liulizhi1031/ProjectEvolution/3D_Model/V0.1_3D_Model/3.5寸屏幕模块/img_dev_2.png

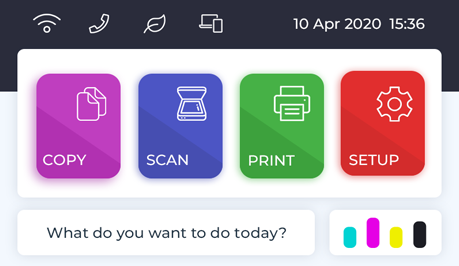
3D_Model/V0.1_3D_Model/3.5寸屏幕模块/img_dev_2.png
