liulizhi1031/ProjectEvolution/3D_Model/V0.1_3D_Model/Frsky-R9M/Render.jpg

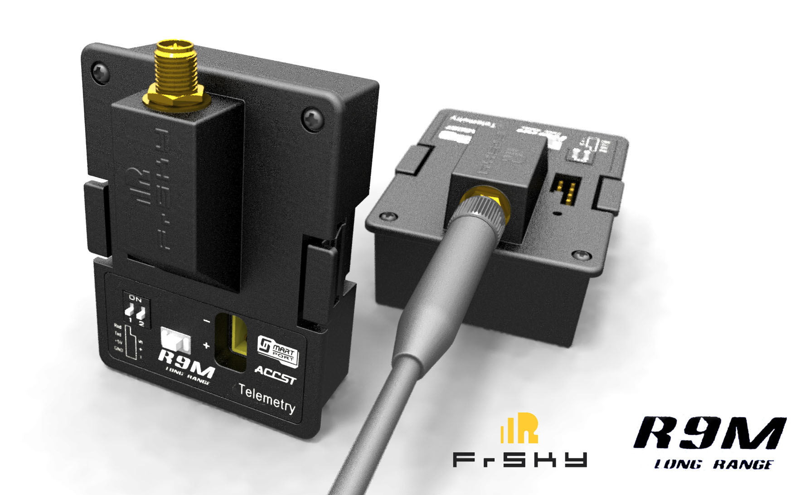
3D_Model/V0.1_3D_Model/Frsky-R9M/Render.jpg
