liulizhi1031/ProjectEvolution/3D_Model/V0.1_3D_Model/GPS-TS100/IMG_20190112_132327.jpg

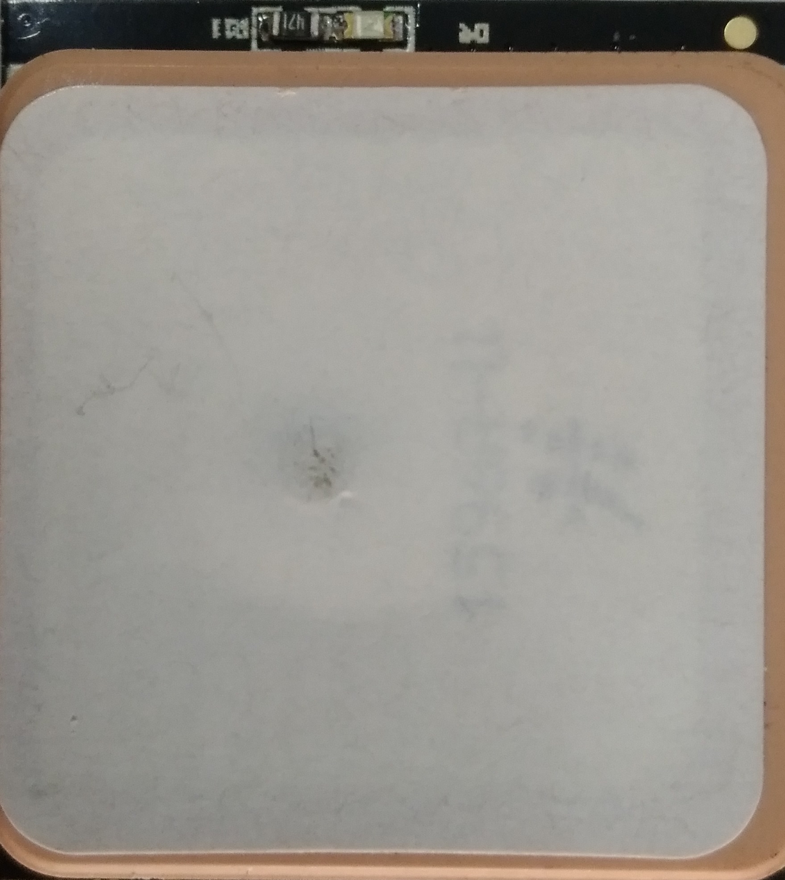
3D_Model/V0.1_3D_Model/GPS-TS100/IMG_20190112_132327.jpg
