liulizhi1031/ProjectEvolution/3D_Model/V0.1_3D_Model/SWD模块/副板正面.JPG

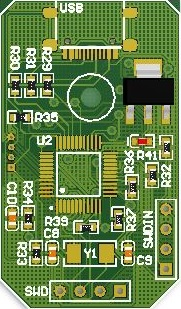
3D_Model/V0.1_3D_Model/SWD模块/副板正面.JPG
