liulizhi1031/ProjectEvolution/Reference/3.5inch_MCU_LCD/3.5inch_MRB3511_Size.png

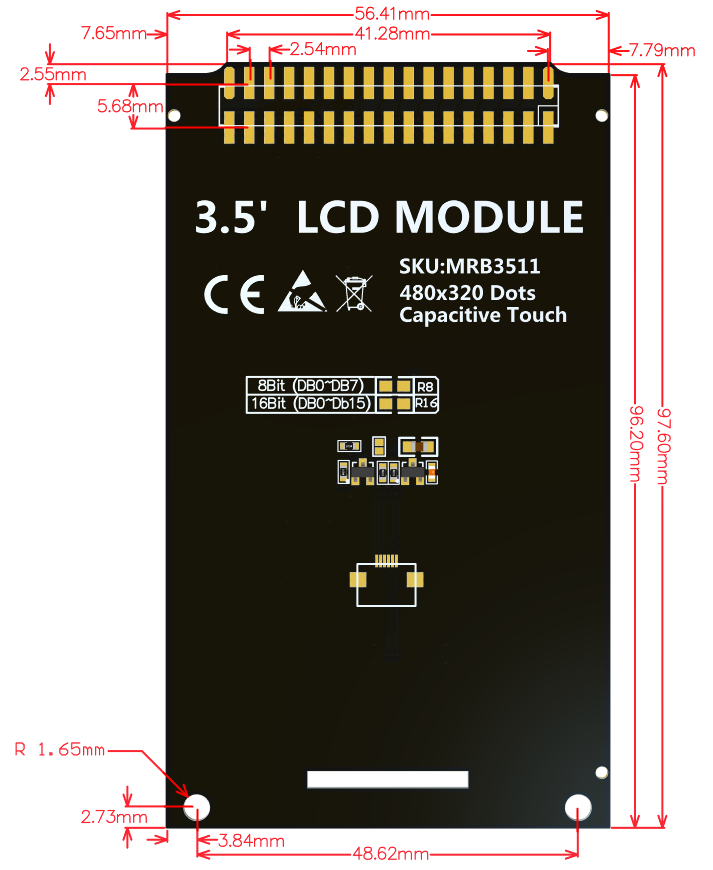
Reference/3.5inch_MCU_LCD/3.5inch_MRB3511_Size.png
