liulizhi1031/ProjectEvolution/3D_Model/V0.1_3D_Model/GPS-TS100/GPS-TS100.SLDPRT

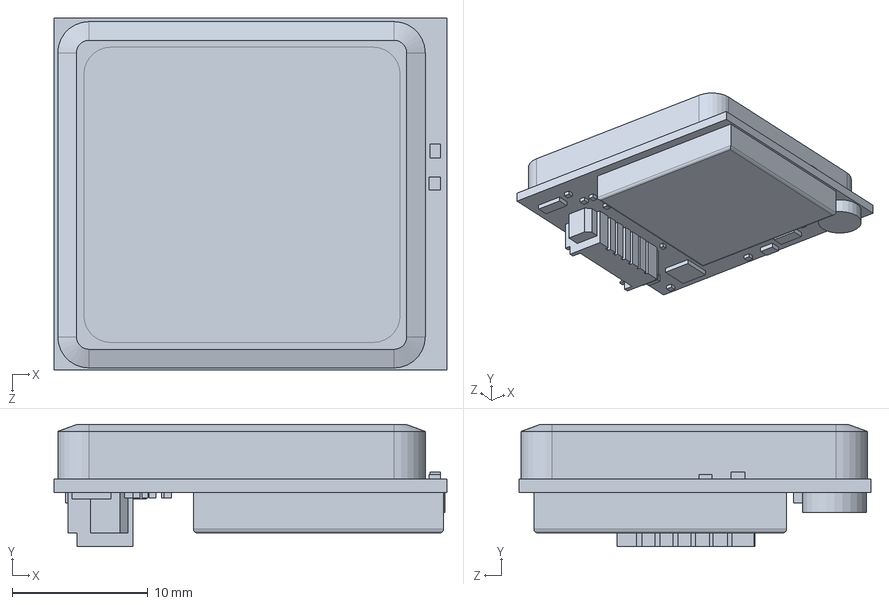
[picture p53: CAD file, 2021-01-28]
3D_Model/V0.1_3D_Model/GPS-TS100/GPS-TS100.SLDPRT
29.0 x 9.01 x 26.0 mm
