liulizhi1031/ProjectEvolution/3D_Model/V0.1_3D_Model/keyboard/滑动开关/滑动开关.SLDPRT

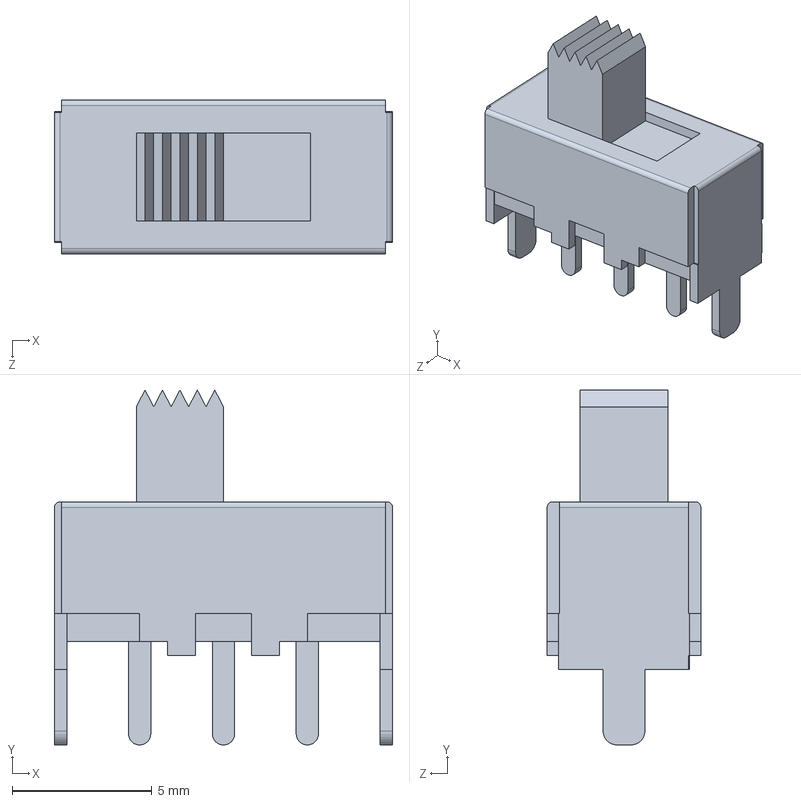
[picture p54: CAD file, 2021-01-28]
3D_Model/V0.1_3D_Model/keyboard/滑动开关/滑动开关.SLDPRT
12.1 x 12.7 x 5.50 mm
