liulizhi1031/ProjectEvolution/3D_Model/V0.1_3D_Model/mini_MP3/MP3_mini.SLDPRT

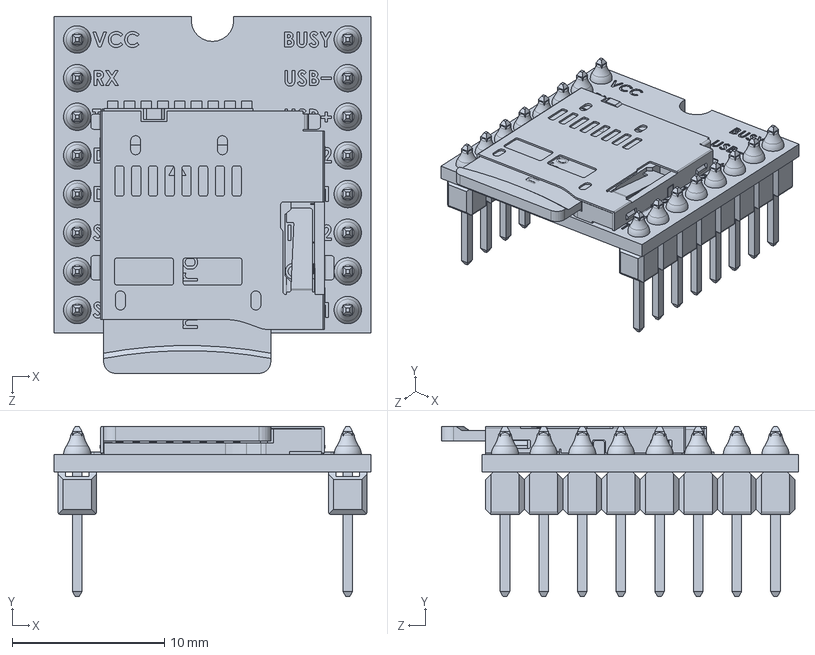
[picture p55: CAD file, 2021-01-28]
3D_Model/V0.1_3D_Model/mini_MP3/MP3_mini.SLDPRT
20.8 x 11.2 x 23.5 mm
