liulizhi1031/ProjectEvolution/3D_Model/V0.1_3D_Model/NRF24l01/E01-ML01DP5.SLDPRT

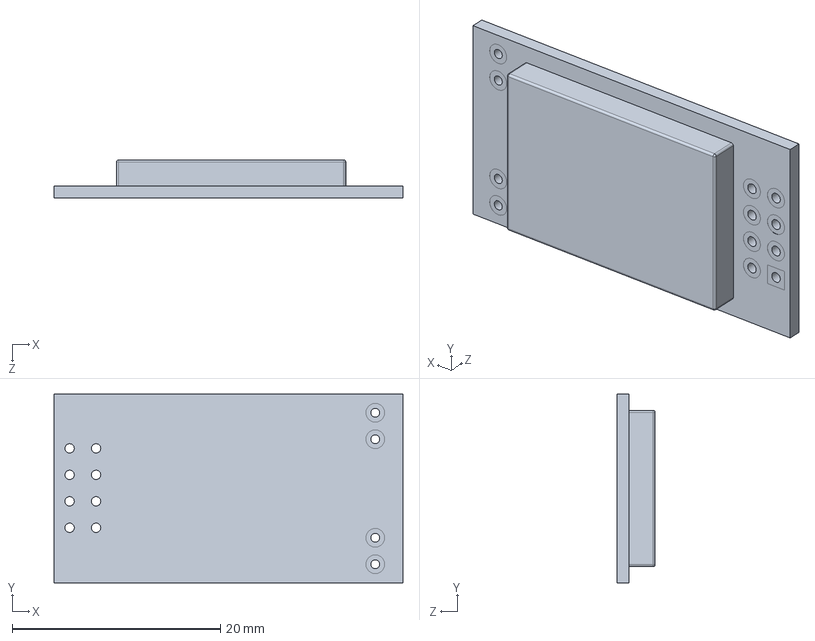
[picture p56: CAD file, 2021-01-28]
3D_Model/V0.1_3D_Model/NRF24l01/E01-ML01DP5.SLDPRT
33.5 x 18.1 x 3.69 mm
