liulizhi1031/ProjectEvolution/3D_Model/V0.1_3D_Model/STL/ANTENNA_STAND.STL

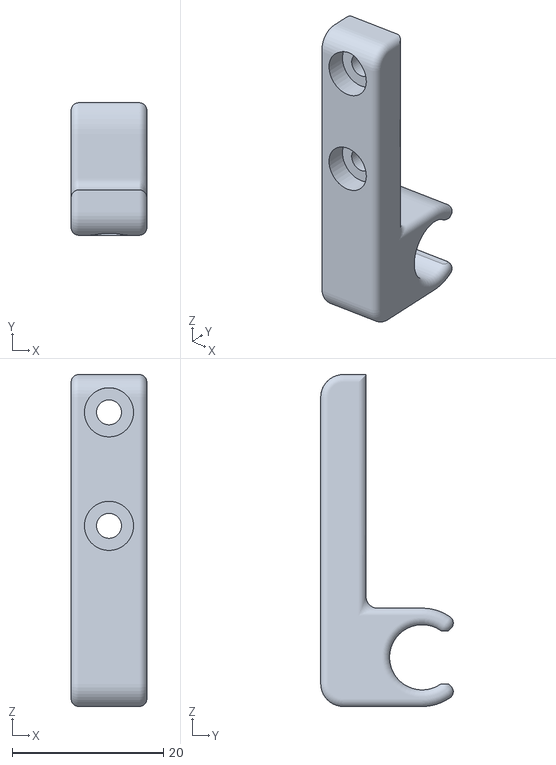
[picture p58: CAD file, 2021-02-08]
3D_Model/V0.1_3D_Model/STL/ANTENNA_STAND.STL
10.0 x 17.5 x 43.9
