liulizhi1031/ProjectEvolution/3D_Model/V0.1_3D_Model/SWD模块/1.27mmHeader.SLDPRT

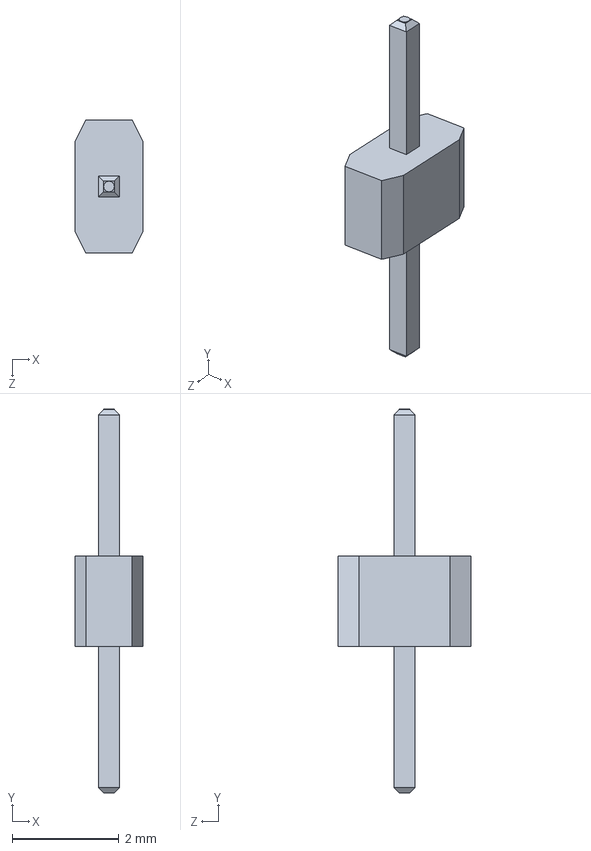
[picture p59: CAD file, 2021-01-28]
3D_Model/V0.1_3D_Model/SWD模块/1.27mmHeader.SLDPRT
1.27 x 7.21 x 2.50 mm
