liulizhi1031/ProjectEvolution/3D_Model/V0.1_3D_Model/SWD模块/stm32f103c8t6-1.snapshot.1/STM32-LQFP48.SLDPRT

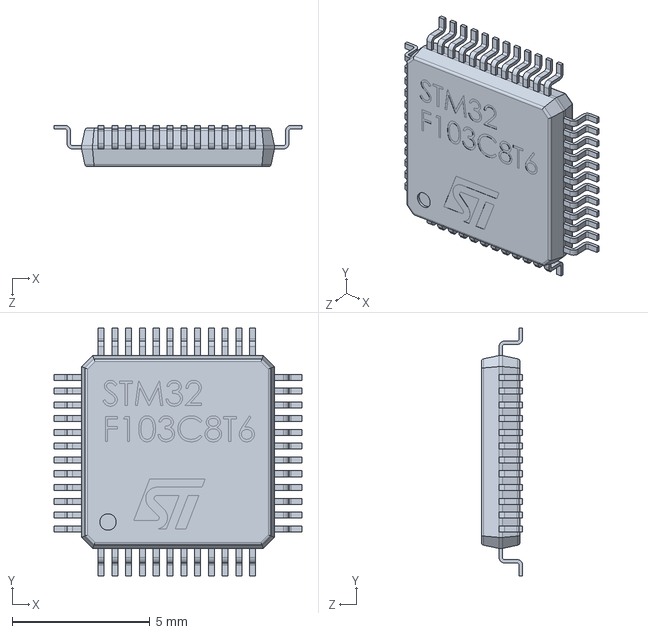
[picture p61: CAD file, 2021-01-28]
3D_Model/V0.1_3D_Model/SWD模块/stm32f103c8t6-1.snapshot.1/STM32-LQFP48.SLDPRT
9.00 x 9.00 x 1.50 mm
