liulizhi1031/ProjectEvolution/3D_Model/V0.1_3D_Model/SWD模块/USB_TYPE_C/USB Type C Port (SMD Type).STEP

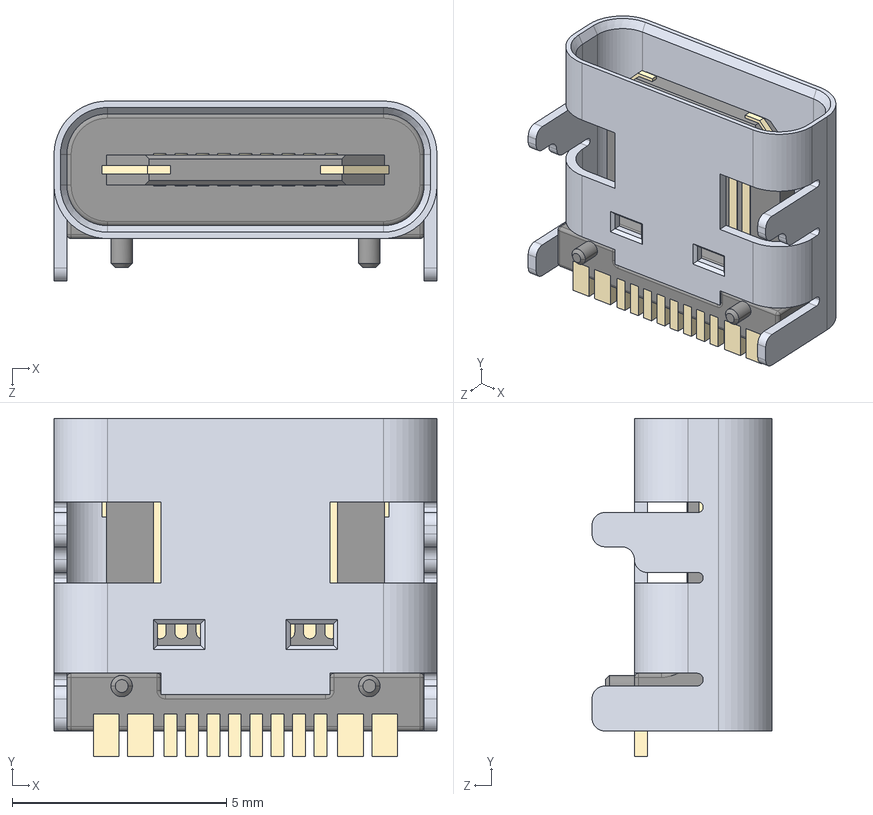
[picture p62: CAD file, 2021-01-28]
3D_Model/V0.1_3D_Model/SWD模块/USB_TYPE_C/USB Type C Port (SMD Type).STEP
8.94 x 7.90 x 4.20 mm
