liulizhi1031/ProjectEvolution/3D_Model/V0.1_3D_Model/下壳.SLDPRT

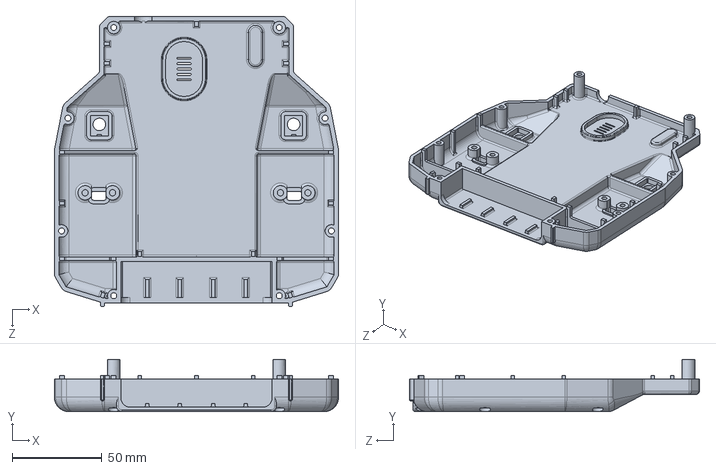
[picture p63: CAD file, 2021-02-08]
3D_Model/V0.1_3D_Model/下壳.SLDPRT
158.0 x 29.0 x 161.2 mm
