liulizhi1031/ProjectEvolution/3D_Model/V0.1_3D_Model/对比模型/Mavic Air 2 Controller.SLDPRT

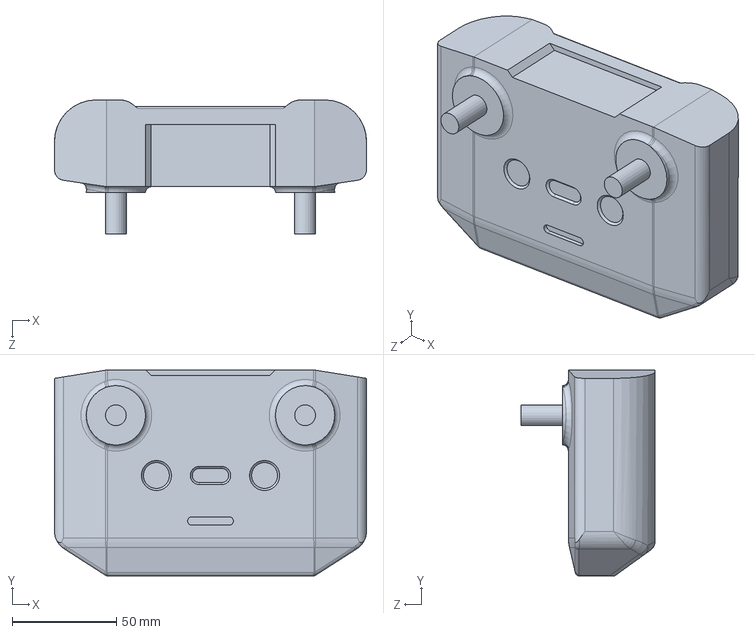
[picture p64: CAD file, 2021-01-28]
3D_Model/V0.1_3D_Model/对比模型/Mavic Air 2 Controller.SLDPRT
150.0 x 99.0 x 64.5 mm
