liulizhi1031/ProjectEvolution/3D_Model/V0.1_3D_Model/按键板/JST connector 1x3.SLDPRT

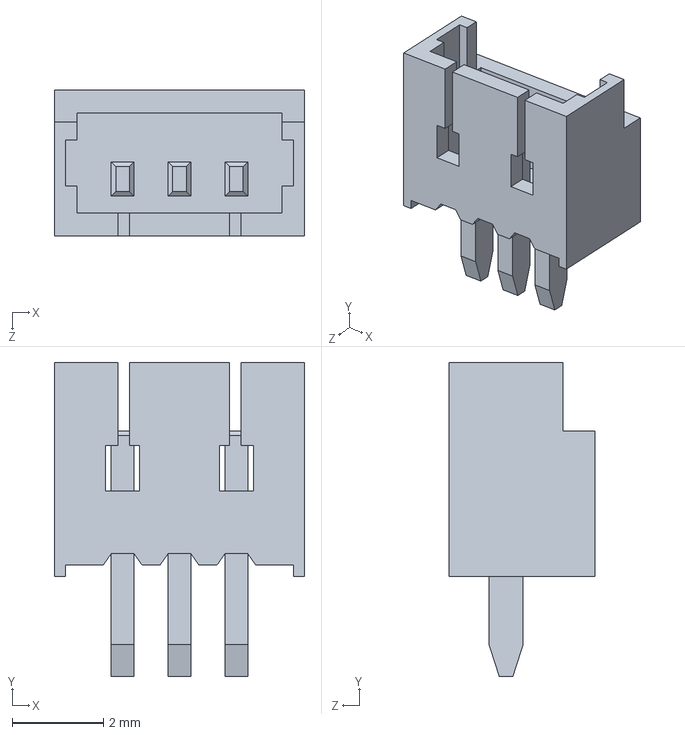
[picture p65: CAD file, 2021-01-28]
3D_Model/V0.1_3D_Model/按键板/JST connector 1x3.SLDPRT
5.50 x 6.90 x 3.20 mm
