liulizhi1031/ProjectEvolution/3D_Model/V0.1_3D_Model/电位器10K/Turn Knob.SLDPRT

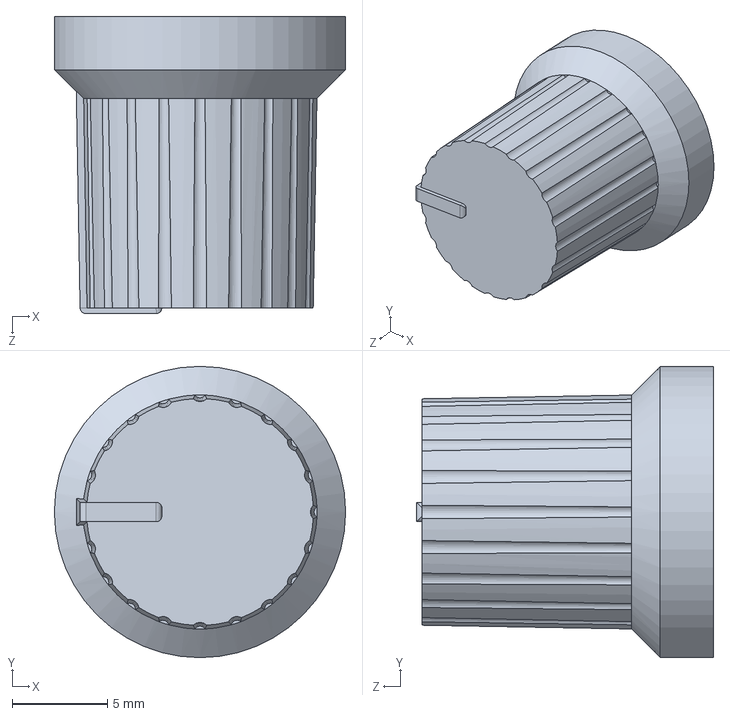
[picture p66: CAD file, 2021-01-30]
3D_Model/V0.1_3D_Model/电位器10K/Turn Knob.SLDPRT
15.3 x 15.3 x 15.6 mm
