liulizhi1031/ProjectEvolution/3D_Model/V0.1_3D_Model/航模摇杆T8SG/摇杆头.SLDPRT

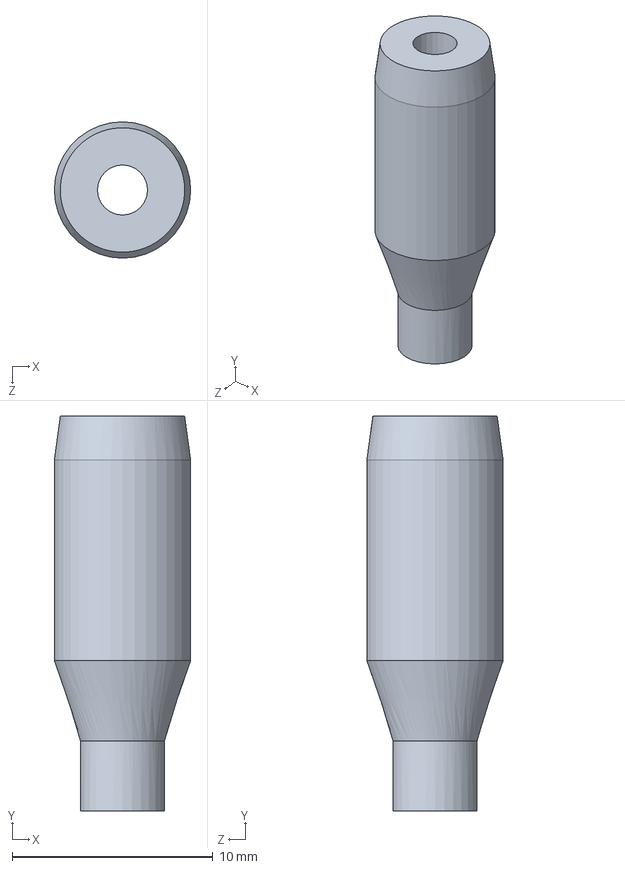
[picture p67: CAD file, 2021-01-28]
3D_Model/V0.1_3D_Model/航模摇杆T8SG/摇杆头.SLDPRT
6.80 x 19.7 x 6.80 mm
