liulizhi1031/ProjectEvolution/PCB/V0.1_PCB/CoreBoard/coreboardV0.1pcb.step

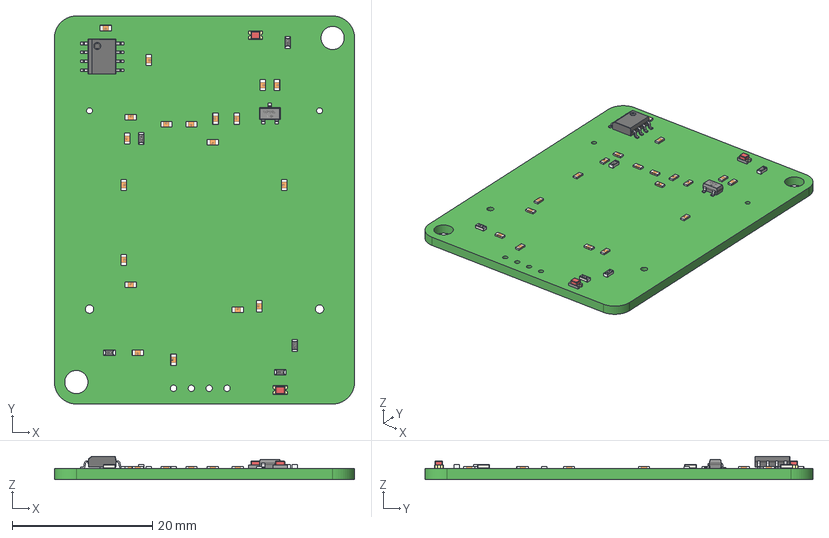
[picture p68: CAD file, 2021-01-28]
PCB/V0.1_PCB/CoreBoard/coreboardV0.1pcb.step
42.8 x 55.3 x 3.34 mm
Board
User_Library-SOIC-8-150_pin_SOIC_SO-150_1 x 8
User_Library-SOIC-8-150_SOIC_150_SOIC_5X4_1
User_Library-0603_SMD_Capacitor x 19
SOT-23
User_Library-RES_1609-0603 x 5
User_Library-led_0805 x 2
