liulizhi1031/ProjectEvolution/PCB/V0.1_PCB/KeyBoard/keyboardV0.1.step

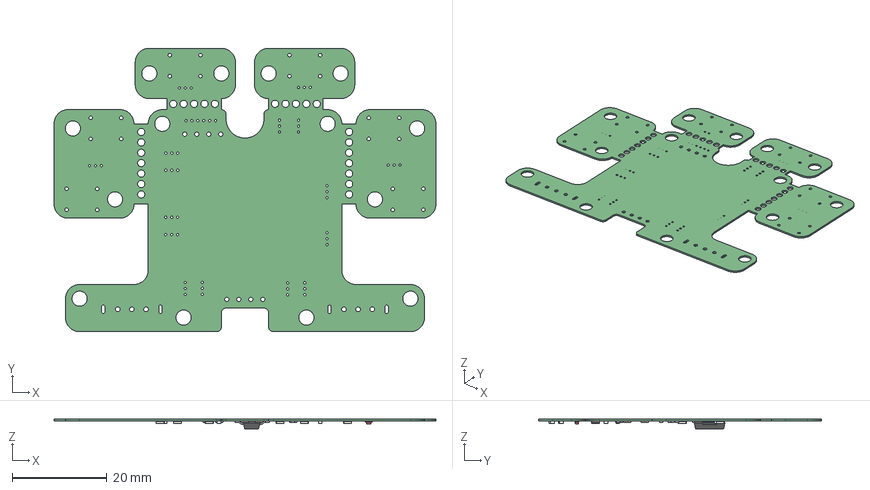
[picture p69: CAD file, 2021-01-28]
PCB/V0.1_PCB/KeyBoard/keyboardV0.1.step
80.8 x 60.0 x 2.05 mm
Board
User_Library-RES_1609-0603 x 14
User_Library-TO-223_1_1
User_Library-TO-223_2_1
User_Library-TO-223_3_1
User_Library-TO-223_4_1
User_Library-TO-223_5_1
User_Library-LED_0603_R_Pocket002
User_Library-LED_0603_R_Pad004
User_Library-LED_0603_R_Fillet
User_Library-LED_0603_R_Pocket001
User_Library-LED_0603_R_Pad
User_Library-0603_SMD_Capacitor x 13
