liulizhi1031/ProjectEvolution/3D_Model/V0.1_3D_Model/3.5寸屏幕模块/PIN254.SLDPRT

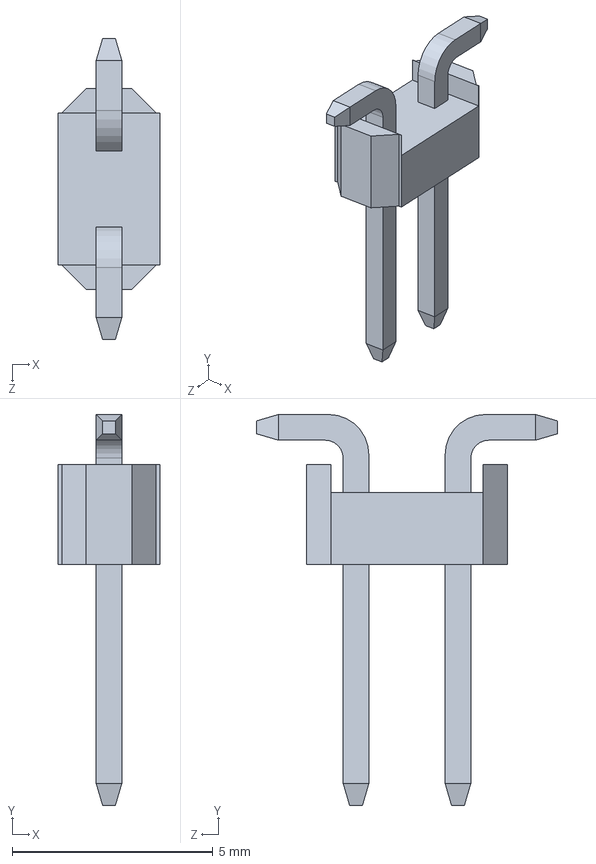
[picture p70: CAD file, 2021-01-28]
3D_Model/V0.1_3D_Model/3.5寸屏幕模块/PIN254.SLDPRT
2.54 x 9.74 x 7.50 mm
