liulizhi1031/ProjectEvolution/3D_Model/V0.1_3D_Model/keyboard/静音按键_.SLDPRT

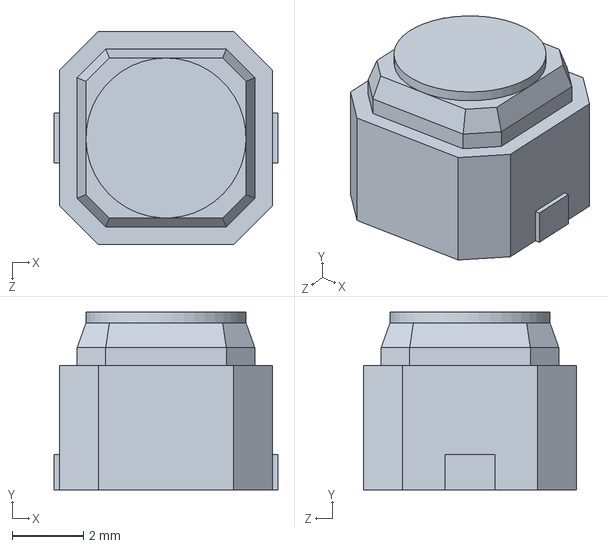
[picture p71: CAD file, 2021-01-28]
3D_Model/V0.1_3D_Model/keyboard/静音按键_.SLDPRT
6.30 x 5.00 x 6.00 mm
