liulizhi1031/ProjectEvolution/3D_Model/V0.1_3D_Model/NRF24l01/2.54MM_4_2PIN.SLDPRT

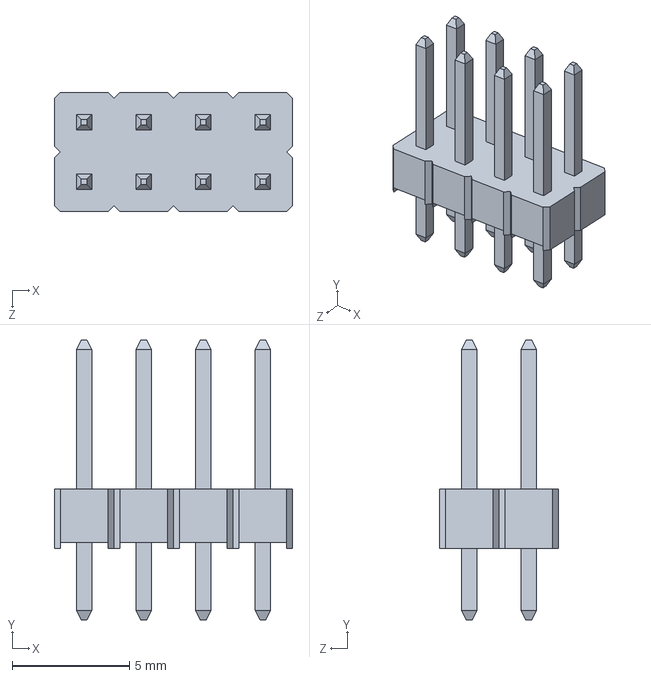
[picture p72: CAD file, 2021-01-28]
3D_Model/V0.1_3D_Model/NRF24l01/2.54MM_4_2PIN.SLDPRT
10.2 x 11.9 x 5.08 mm
