liulizhi1031/ProjectEvolution/3D_Model/V0.1_3D_Model/NRF24l01/棒状天线/Antenna.STEP

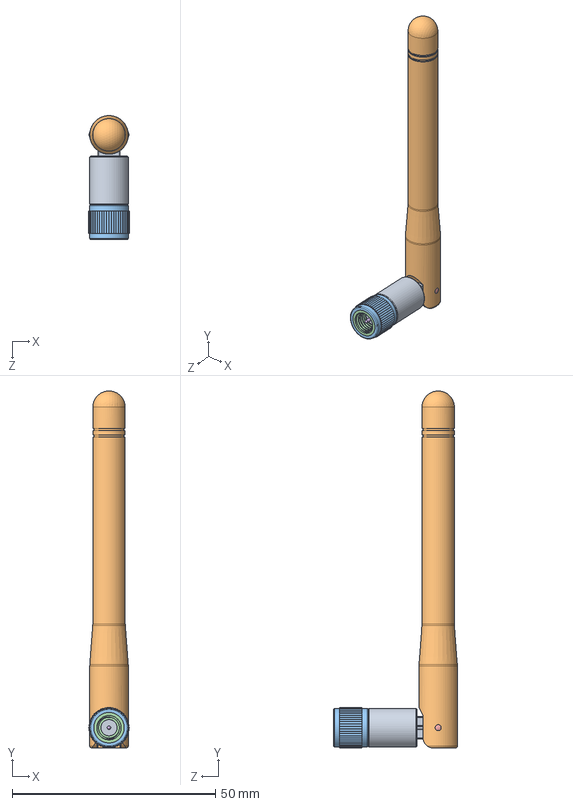
[picture p73: CAD file, 2021-01-28]
3D_Model/V0.1_3D_Model/NRF24l01/棒状天线/Antenna.STEP
10.00 x 87.9 x 30.5 mm
Bottom_Radio_Antenna
Top_Radio_Antenna
Screw_Radio_Antenna
Insert_Radio_Antenna
Pin_Radio_Antenna x 2
Wire_Top_Radio_Antenna
Wire_Radio_Antenna
