liulizhi1031/ProjectEvolution/3D_Model/V0.1_3D_Model/STL/BATTERY_COVER.STL

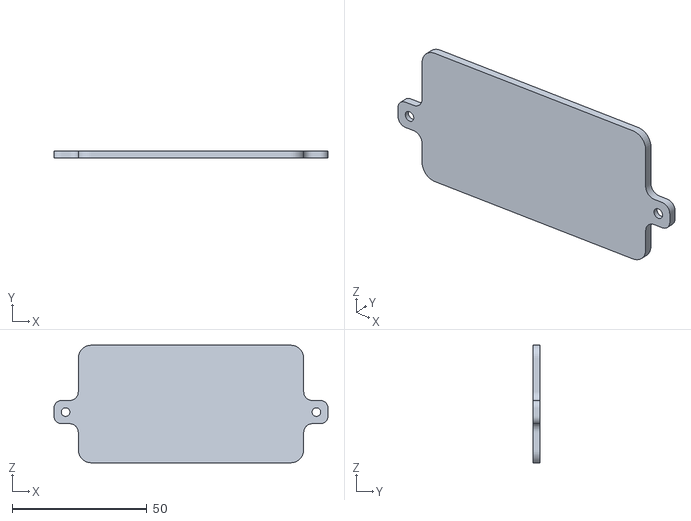
[picture p74: CAD file, 2021-02-05]
3D_Model/V0.1_3D_Model/STL/BATTERY_COVER.STL
101.6 x 2.50 x 43.6
