liulizhi1031/ProjectEvolution/3D_Model/V0.1_3D_Model/按键板/Tactal Switch -Thru (6mmx 6mmx5.0mm).SLDPRT

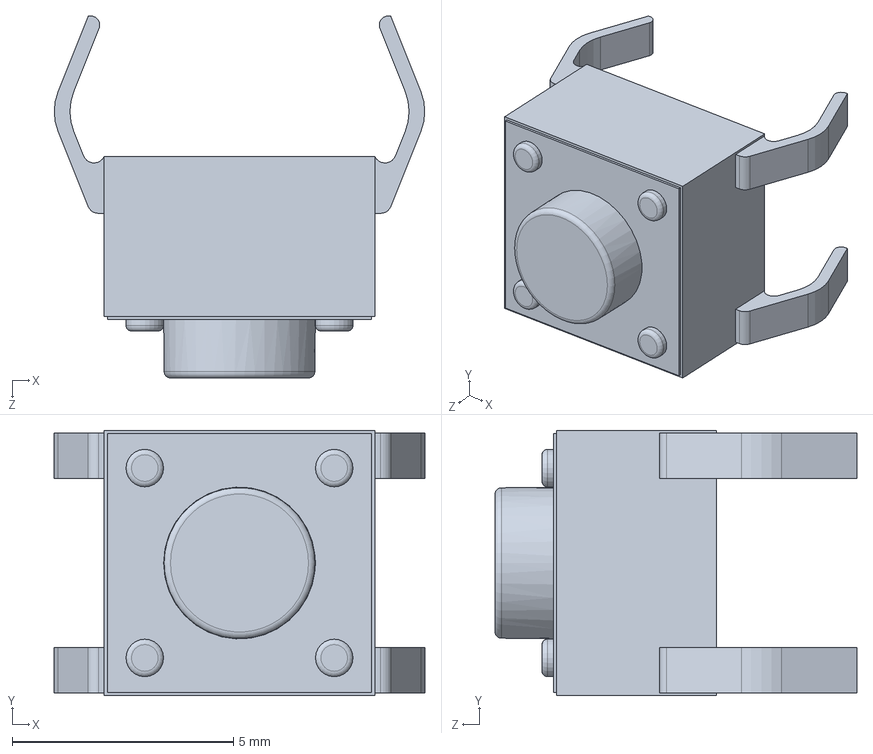
[picture p75: CAD file, 2021-01-28]
3D_Model/V0.1_3D_Model/按键板/Tactal Switch -Thru (6mmx 6mmx5.0mm).SLDPRT
8.37 x 5.99 x 8.18 mm
