liulizhi1031/ProjectEvolution/3D_Model/V0.1_3D_Model/电位器10K/PTD904.SLDPRT

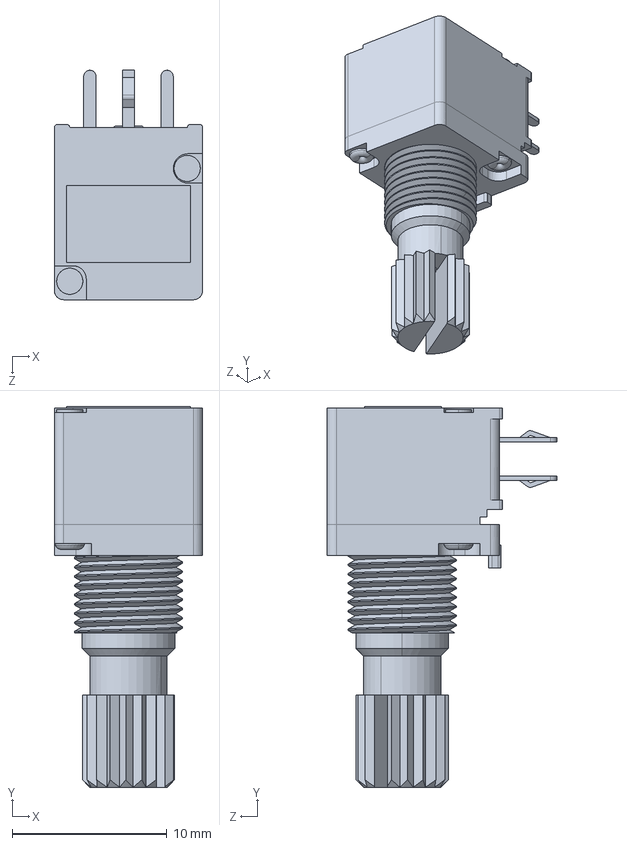
[picture p76: CAD file, 2021-01-28]
3D_Model/V0.1_3D_Model/电位器10K/PTD904.SLDPRT
9.60 x 24.6 x 14.9 mm
