liulizhi1031/ProjectEvolution/3D_Model/V0.1_3D_Model/航模摇杆T8SG/摇杆中间组件3.SLDPRT

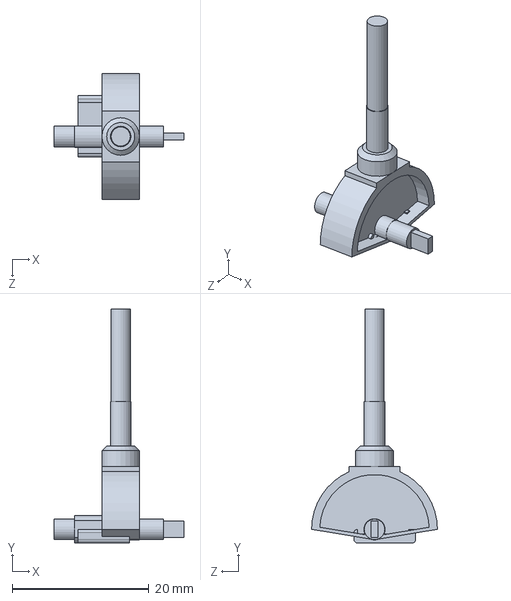
[picture p77: CAD file, 2021-01-28]
3D_Model/V0.1_3D_Model/航模摇杆T8SG/摇杆中间组件3.SLDPRT
19.0 x 34.2 x 18.4 mm
