liulizhi1031/ProjectEvolution/3D_Model/V0.1_3D_Model/Frsky-R9M/FrSky_R9M.SLDPRT

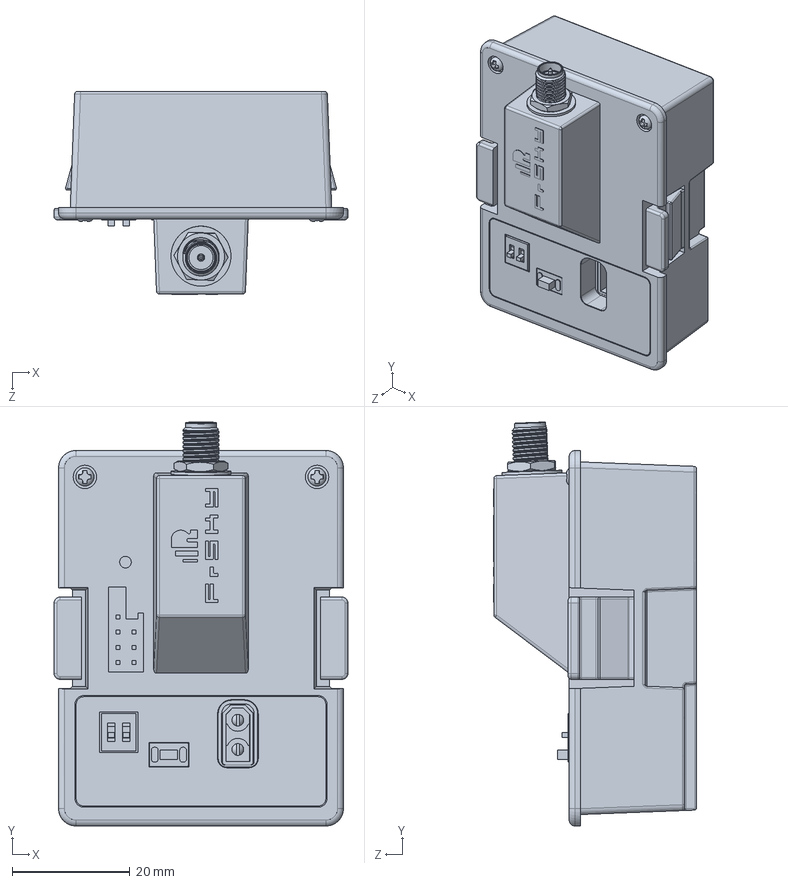
[picture p78: CAD file, 2021-01-28]
3D_Model/V0.1_3D_Model/Frsky-R9M/FrSky_R9M.SLDPRT
50.0 x 68.7 x 34.6 mm
