liulizhi1031/ProjectEvolution/3D_Model/V0.1_3D_Model/NRF24l01/棒状天线/Wire_Radio_Antenna.SLDPRT

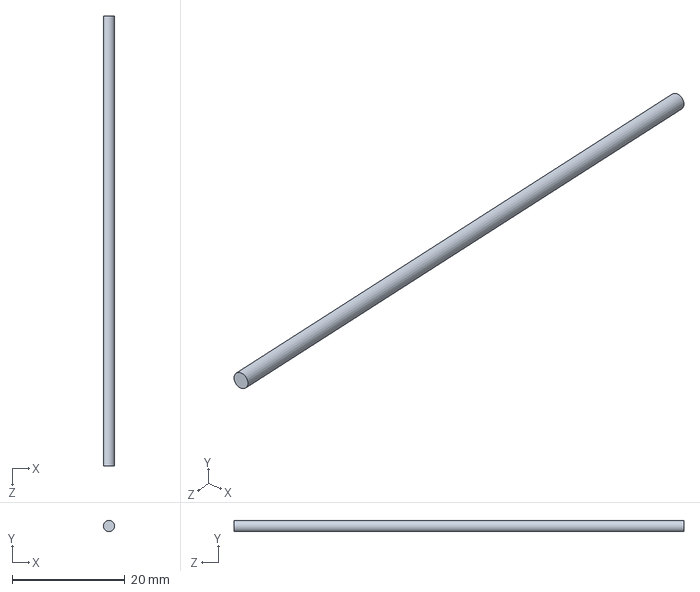
[picture p79: CAD file, 2021-01-28]
3D_Model/V0.1_3D_Model/NRF24l01/棒状天线/Wire_Radio_Antenna.SLDPRT
2.00 x 2.00 x 80.0 mm
