liulizhi1031/ProjectEvolution/3D_Model/V0.1_3D_Model/STL/KNOB.STL

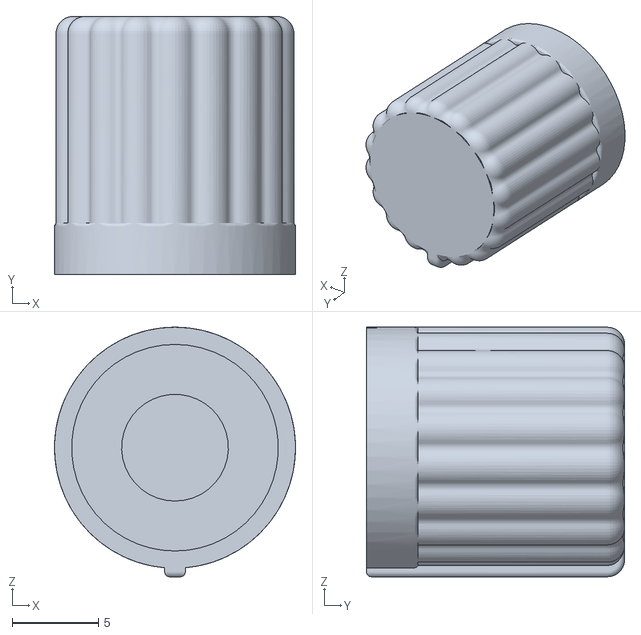
[picture p80: CAD file, 2021-02-05]
3D_Model/V0.1_3D_Model/STL/KNOB.STL
14.0 x 15.0 x 14.5
