liulizhi1031/ProjectEvolution/3D_Model/V0.1_3D_Model/按键帽.SLDPRT

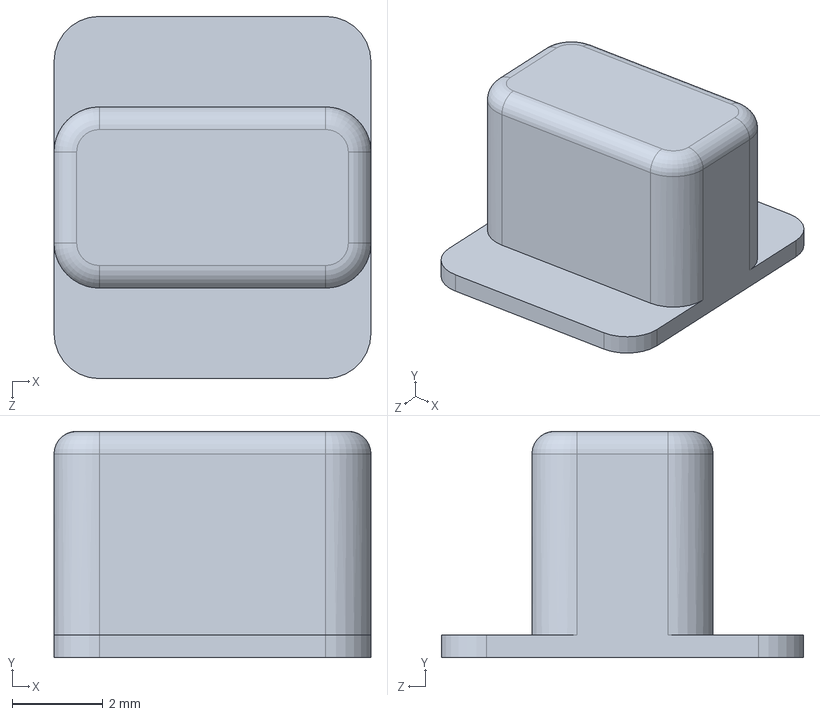
[picture p81: CAD file, 2021-02-05]
3D_Model/V0.1_3D_Model/按键帽.SLDPRT
7.00 x 5.00 x 8.00 mm
