liulizhi1031/ProjectEvolution/3D_Model/V0.1_3D_Model/NRF24l01/Amphenol 132415.step.SLDPRT

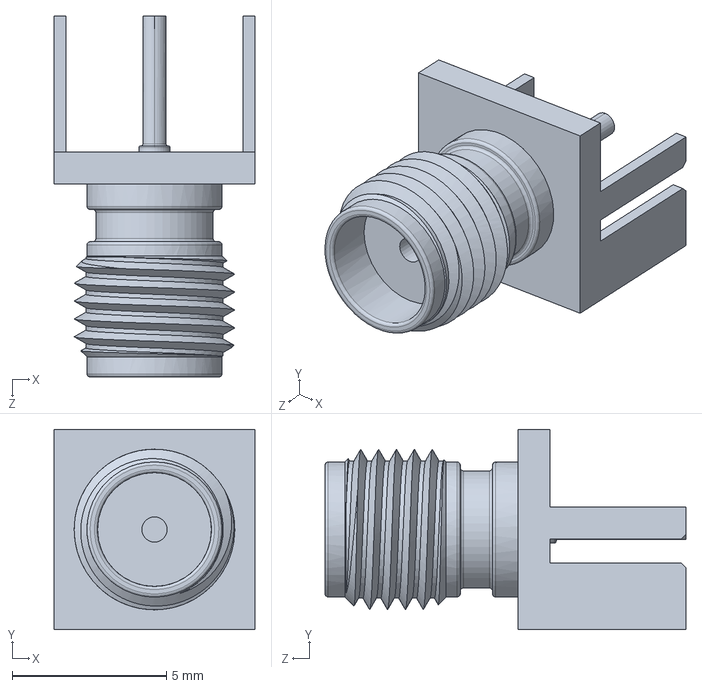
[picture p82: CAD file, 2021-01-28]
3D_Model/V0.1_3D_Model/NRF24l01/Amphenol 132415.step.SLDPRT
6.50 x 6.49 x 11.7 mm
