liulizhi1031/ProjectEvolution/3D_Model/V0.1_3D_Model/NRF24l01/棒状天线/Top_Radio_Antenna.SLDPRT

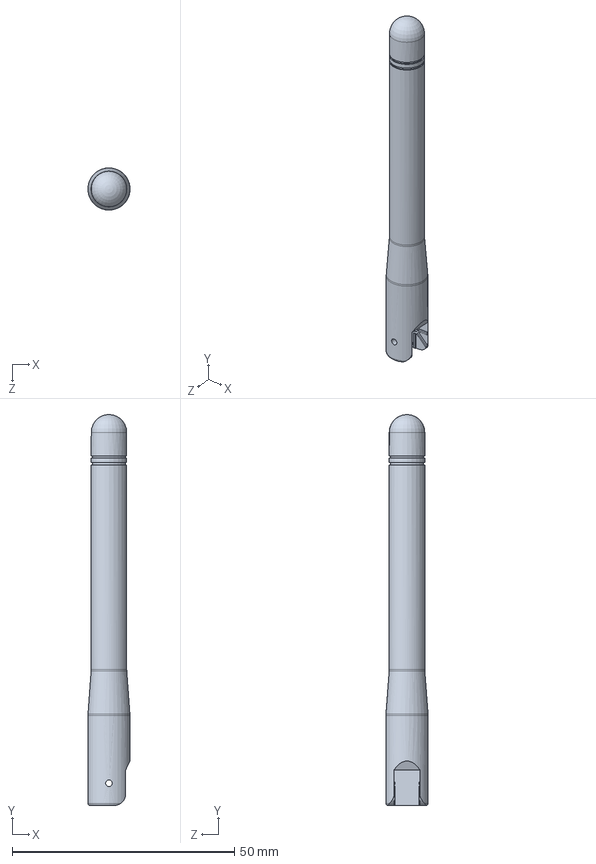
[picture p83: CAD file, 2021-01-28]
3D_Model/V0.1_3D_Model/NRF24l01/棒状天线/Top_Radio_Antenna.SLDPRT
9.47 x 87.9 x 9.50 mm
