liulizhi1031/ProjectEvolution/3D_Model/V0.1_3D_Model/STL/GPS_COVER.STL

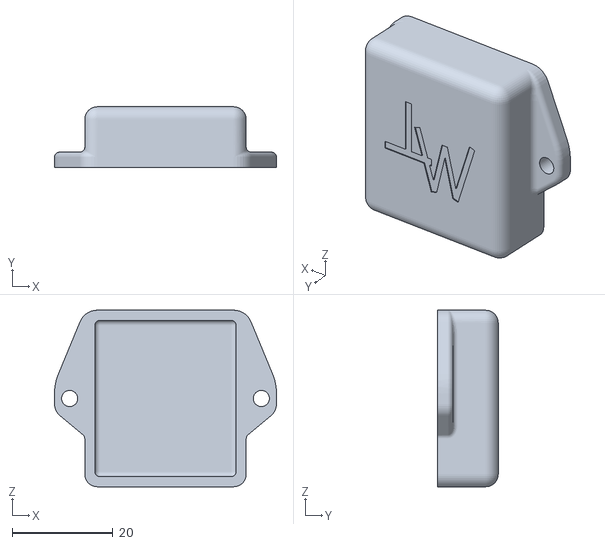
[picture p84: CAD file, 2021-02-05]
3D_Model/V0.1_3D_Model/STL/GPS_COVER.STL
44.0 x 12.0 x 35.0
