liulizhi1031/ProjectEvolution/3D_Model/V0.1_3D_Model/SWD模块/AMS1117-3.3V/JST - GH - Thru (V) - 2Pin - 1.25mm.stp.SLDPRT

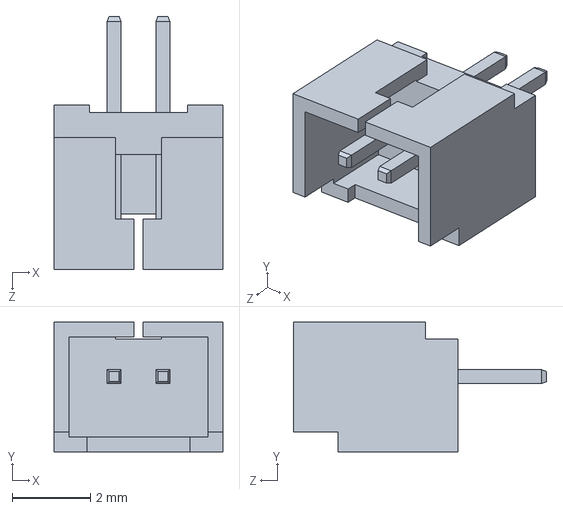
[picture p85: CAD file, 2021-01-28]
3D_Model/V0.1_3D_Model/SWD模块/AMS1117-3.3V/JST - GH - Thru (V) - 2Pin - 1.25mm.stp.SLDPRT
4.32 x 3.33 x 6.48 mm
