liulizhi1031/ProjectEvolution/3D_Model/V0.1_3D_Model/SWD模块/SWD模块.SLDPRT

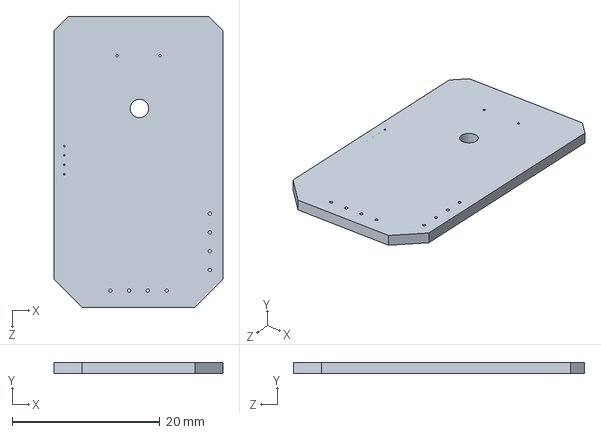
[picture p86: CAD file, 2021-01-28]
3D_Model/V0.1_3D_Model/SWD模块/SWD模块.SLDPRT
22.9 x 1.50 x 39.4 mm
