liulizhi1031/ProjectEvolution/3D_Model/V0.1_3D_Model/航模摇杆T8SG/轴承.SLDPRT

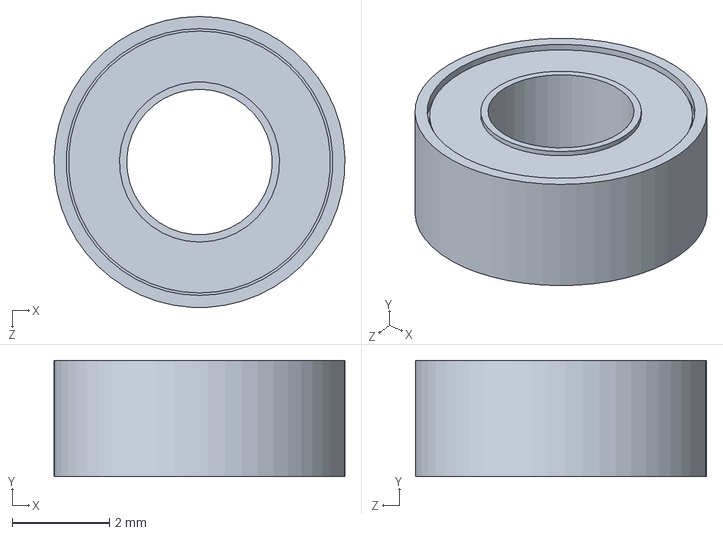
[picture p87: CAD file, 2021-01-28]
3D_Model/V0.1_3D_Model/航模摇杆T8SG/轴承.SLDPRT
6.00 x 2.40 x 6.00 mm
