liulizhi1031/ProjectEvolution/3D_Model/V0.1_3D_Model/NRF24l01/棒状天线/Wire_Top_Radio_Antenna.SLDPRT

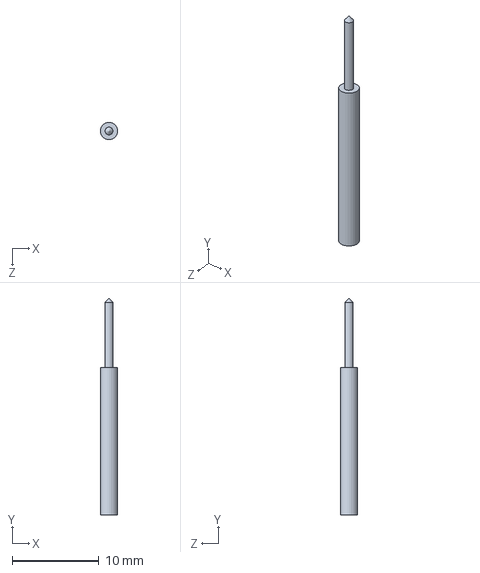
[picture p88: CAD file, 2021-01-28]
3D_Model/V0.1_3D_Model/NRF24l01/棒状天线/Wire_Top_Radio_Antenna.SLDPRT
2.00 x 25.0 x 2.00 mm
