liulizhi1031/ProjectEvolution/3D_Model/V0.1_3D_Model/STL/POW_KEY.STL

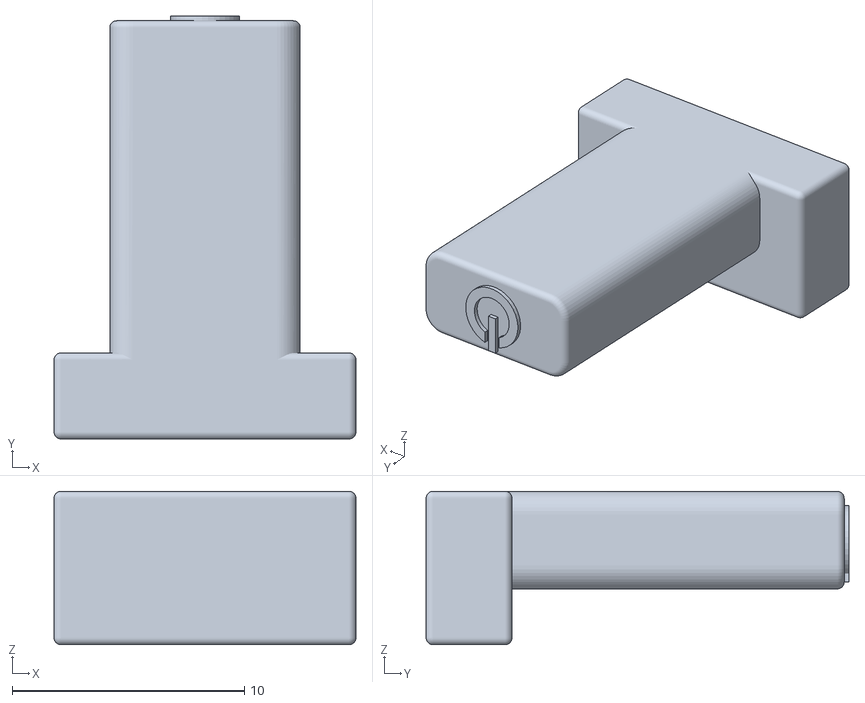
[picture p89: CAD file, 2021-02-05]
3D_Model/V0.1_3D_Model/STL/POW_KEY.STL
13.0 x 18.2 x 6.60
