liulizhi1031/ProjectEvolution/3D_Model/V0.1_3D_Model/航模摇杆T8SG/摇杆中间组件1.SLDPRT

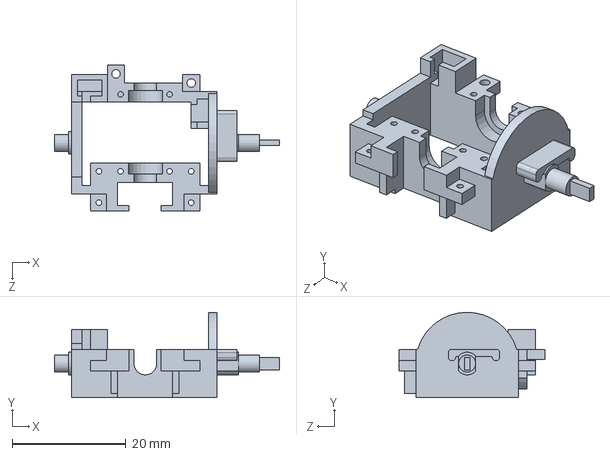
[picture p91: CAD file, 2021-01-28]
3D_Model/V0.1_3D_Model/航模摇杆T8SG/摇杆中间组件1.SLDPRT
39.5 x 15.0 x 25.7 mm
