liulizhi1031/ProjectEvolution/3D_Model/V0.1_3D_Model/航模摇杆T8SG/摇杆中间组件2.SLDPRT

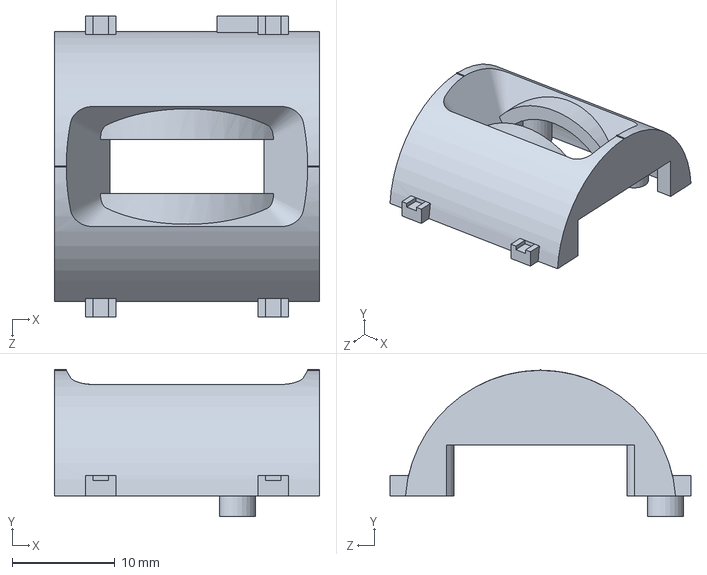
[picture p93: CAD file, 2021-01-28]
3D_Model/V0.1_3D_Model/航模摇杆T8SG/摇杆中间组件2.SLDPRT
25.8 x 14.3 x 29.3 mm
