liulizhi1031/ProjectEvolution/3D_Model/V0.1_3D_Model/NRF24l01/棒状天线/Insert_Radio_Antenna.SLDPRT

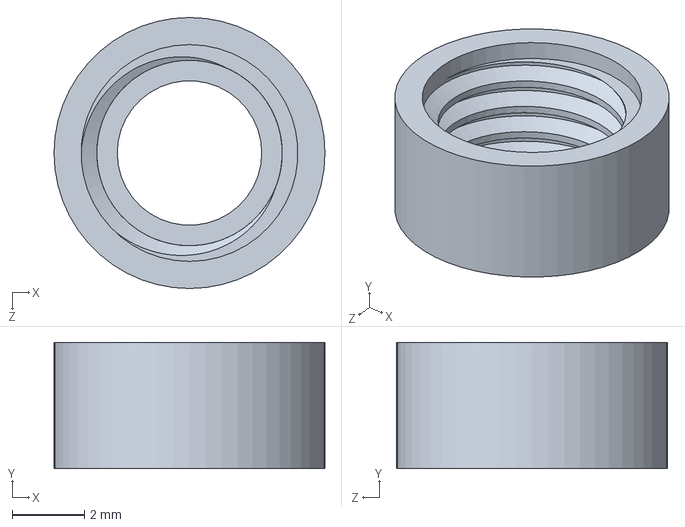
[picture p94: CAD file, 2021-01-28]
3D_Model/V0.1_3D_Model/NRF24l01/棒状天线/Insert_Radio_Antenna.SLDPRT
7.50 x 3.50 x 7.50 mm
