liulizhi1031/ProjectEvolution/3D_Model/V0.1_3D_Model/SWD模块/AMS1117-3.3V/AMS1117.STEP

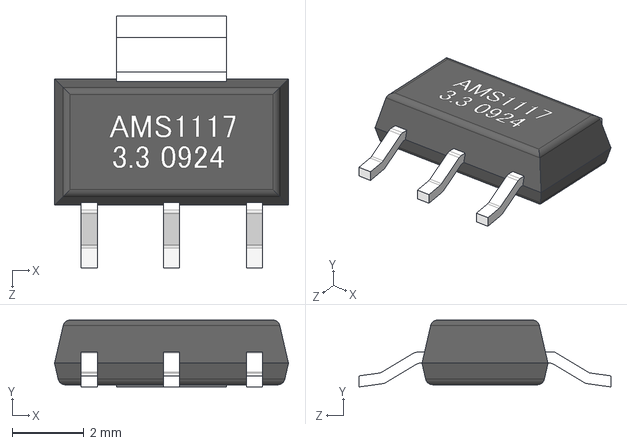
[picture p95: CAD file, 2021-01-28]
3D_Model/V0.1_3D_Model/SWD模块/AMS1117-3.3V/AMS1117.STEP
6.50 x 1.86 x 7.00 mm
