liulizhi1031/ProjectEvolution/3D_Model/V0.1_3D_Model/上壳.SLDPRT

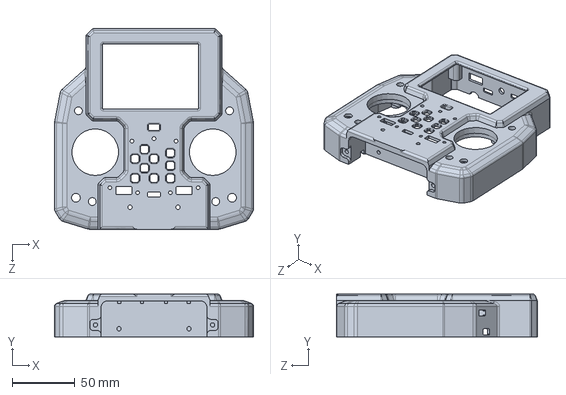
[picture p96: CAD file, 2021-01-30]
3D_Model/V0.1_3D_Model/上壳.SLDPRT
158.0 x 34.0 x 159.2 mm
