liulizhi1031/ProjectEvolution/3D_Model/V0.1_3D_Model/航模摇杆T8SG/电位器.SLDPRT

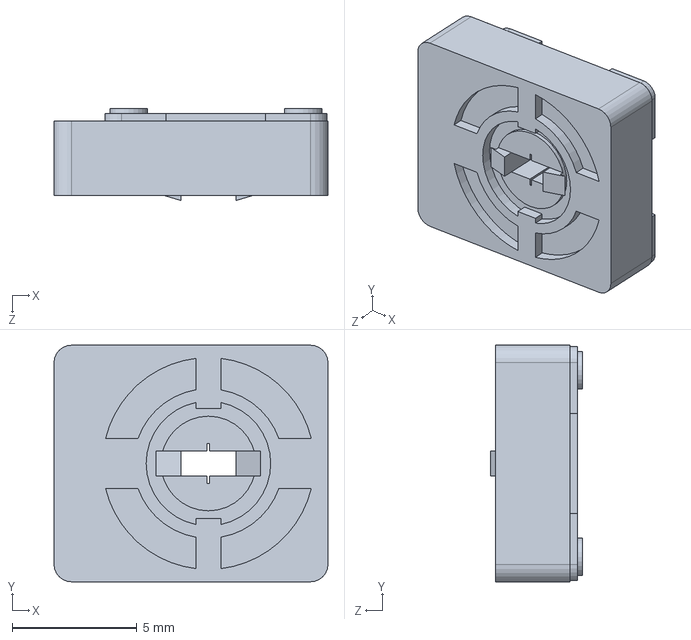
[picture p97: CAD file, 2021-01-28]
3D_Model/V0.1_3D_Model/航模摇杆T8SG/电位器.SLDPRT
11.0 x 9.50 x 3.70 mm
