liulizhi1031/ProjectEvolution/3D_Model/V0.1_3D_Model/NRF24l01/棒状天线/Pin_Radio_Antenna.SLDPRT

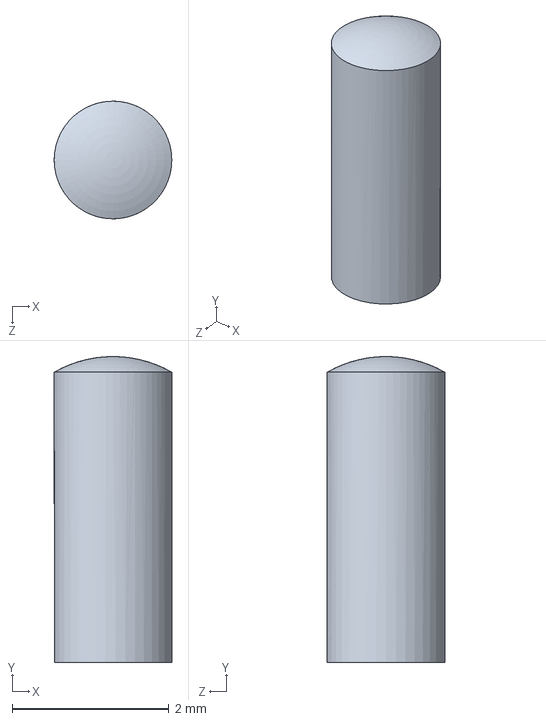
[picture p98: CAD file, 2021-01-28]
3D_Model/V0.1_3D_Model/NRF24l01/棒状天线/Pin_Radio_Antenna.SLDPRT
1.50 x 3.90 x 1.50 mm
