liulizhi1031/ProjectEvolution/3D_Model/V0.1_3D_Model/航模摇杆T8SG/航模摇杆.SLDPRT

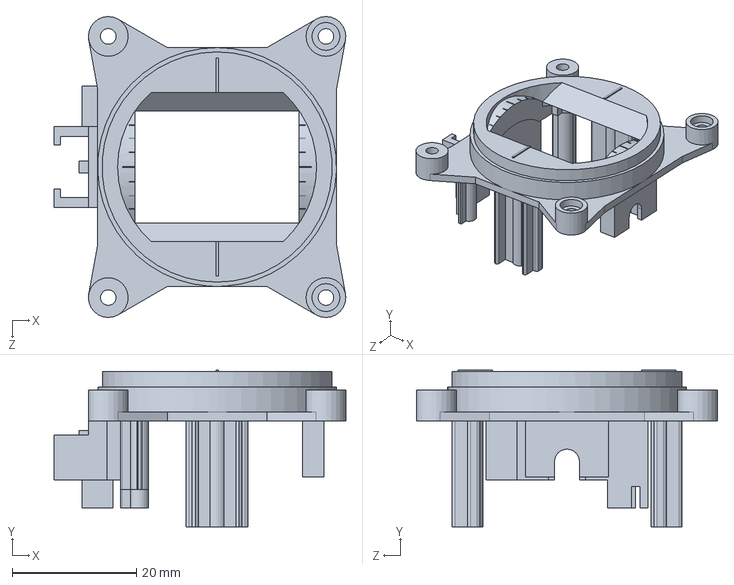
[picture p99: CAD file, 2021-01-28]
3D_Model/V0.1_3D_Model/航模摇杆T8SG/航模摇杆.SLDPRT
46.9 x 25.2 x 48.4 mm
